zwodev/vm1-video-mixer/vm1/cpp/tests/stb-test/rendered-tiles/Cousine-Regular.png

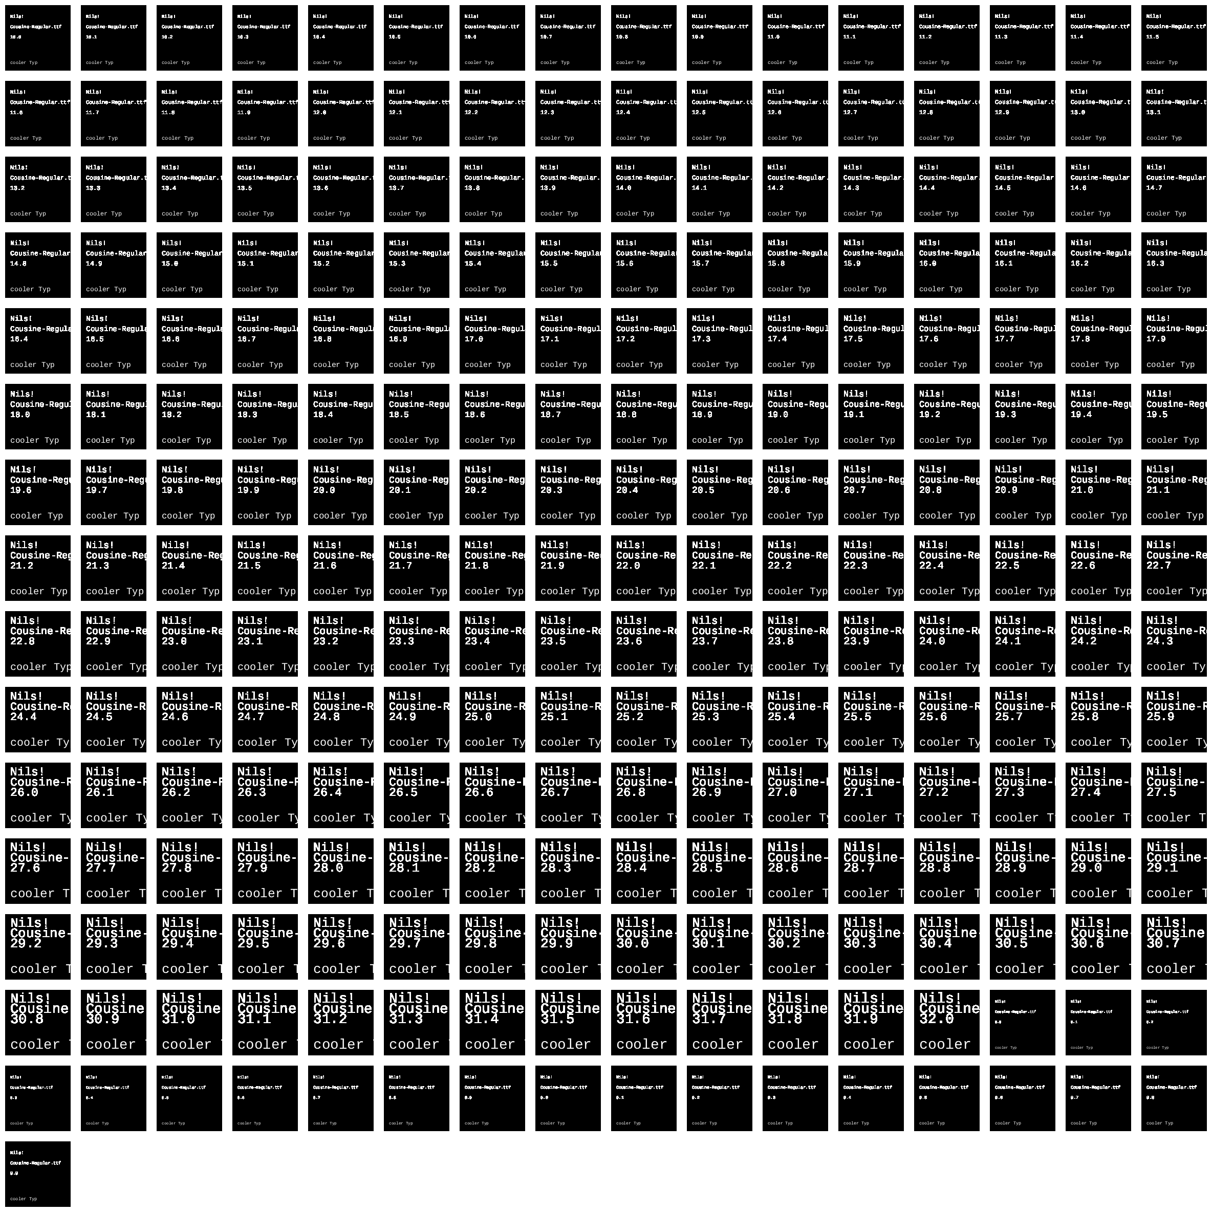
vm1/cpp/tests/stb-test/rendered-tiles/Cousine-Regular.png
