zwodev/vm1-video-mixer/vm1/cpp/source/DeviceController.cpp

/*
 * Copyright (c) 2023-2026 Nils Zweiling & Julian Jungel
 *
 * This file is part of VM-1 which is released under the MIT license.
 * See file LICENSE or go to https://github.com/zwodev/vm1-video-mixer/tree/master/LICENSE
 * for full license details.
 */

#include "DeviceController.h"
#include "VM1DeviceDefinitions.h"
#include <string>
#include <iostream>
#include <fcntl.h>
#include <termios.h>
#include <unistd.h>
#include <cstring>
#include <lgpio.h>

DeviceController::DeviceController(EventBus& eventBus, Registry& registry) : 
    m_eventBus(eventBus),
    m_registry(registry)
{}

DeviceController::~DeviceController(){
    disconnect();
}

// Helper: Set up serial port
bool DeviceController::connect(const std::string& port)
{
    //bool isProVersion = false;

    std::cout << "Failed to open Serial Connection, trying I2C..." << std::endl;
    if(connectI2C()) 
    {
        std::cout << "Connected to VM1-Device via I2C." << std::endl;
        //isProVersion = true;
    } 
    else
    {
        std::cout << "Failed to open I2C, using standard keyboard mode." << std::endl;
        return false;
    }    

    //m_registry.settings().isProVersion = isProVersion;
    return true;
}


bool DeviceController::connectI2C()
{
    m_gpioHandler = lgGpiochipOpen(0); // Usually GPIO chip 0 is correct
    if (m_gpioHandler < 0)
    {
        std::cerr << "Failed to open gpiochip\n";
        return false;
    }
    
    m_i2c_handle = lgI2cOpen(1, 0x08, 0); // bus 1, address 0x08
    if (m_i2c_handle < 0)
    {
        std::cerr << "Failed to open I2C device\n";
        return false;
    }
    return true;
}

void DeviceController::disconnect()
{


    if(m_i2c_handle >= 0)
    {
        lgI2cClose(m_i2c_handle);
        m_i2c_handle = -1;
        
    }

    if (m_gpioHandler >= 0) {
        lgGpiochipClose(m_gpioHandler);
        m_gpioHandler = -1;
    }
}
     

void DeviceController::send(const VM1DeviceState& vm1DeviceState)
{
    // Do not send state when nothing has changed (aka hash is the same)
    size_t hash = vm1DeviceState.hash();
    if (hash == m_lastHash)
        return;

    m_lastHash = hash;

    if (m_i2c_handle >= 0) 
    {
        lgI2cWriteDevice(m_i2c_handle, reinterpret_cast<const char*>(&vm1DeviceState), sizeof(VM1DeviceState));
    }

}

void DeviceController::requestVM1DeviceBuffer() 
{
    if(m_i2c_handle < 0) return;
    
    DeviceBuffer deviceBuffer;
    int count = lgI2cReadDevice(m_i2c_handle, reinterpret_cast<char*>(&deviceBuffer), sizeof(DeviceBuffer));
    if (count != sizeof(DeviceBuffer))
    {
        std::cerr << "Failed to read from I2C device\n";
    }
    else
    {
        bool isFnPressed = deviceBuffer.fnPressed;
        int buttonId = -1;

        for(uint8_t i = 0; i < sizeof(deviceBuffer.buttonEvents)/sizeof(ButtonEvent); i++)
        {
            buttonId = deviceBuffer.buttonEvents[i].buttonId;

            if(!isFnPressed) // if FN not pressed
            {
                switch(deviceBuffer.buttonEvents[i].eventType) 
                {
                    case EDIT_BUTTON_EVENT:
                        m_eventBus.publish(EditModeEvent(buttonId));
                        break;
                    case MEDIA_BUTTON_EVENT: {
                        int mediaSlotId = (m_registry.inputMappings().focusedBank * MEDIA_BUTTON_COUNT) + buttonId;
                        m_eventBus.publish(MediaSlotEvent(mediaSlotId, true));
                        break; }

                    case NAVIGATION_BUTTON_EVENT:
                        if(buttonId == NAVIGATION_BUTTON_RIGHT)
                        {
                            m_eventBus.publish(NavigationEvent(NavigationEvent::Type::NavigationEnter));
                        }
                        else if (buttonId == NAVIGATION_BUTTON_LEFT)
                        {
                            m_eventBus.publish(NavigationEvent(NavigationEvent::Type::NavigationExit));
                        }
                        break;
                    case ROTARY_EVENT:
                        if (buttonId == PRIMARY_ENCODER_CCW)
                        {
                            m_eventBus.publish(NavigationEvent(NavigationEvent::Type::NavigationUp));
                        }
                        else if (buttonId == PRIMARY_ENCODER_CW)
                        {
                            m_eventBus.publish(NavigationEvent(NavigationEvent::Type::NavigationDown));
                        }
                        else if (buttonId == SECONDARY_ENCODER_CCW)
                        {
                            m_eventBus.publish(NavigationEvent(NavigationEvent::Type::NavigationAuxUp));
                        }
                        else if (buttonId == SECONDARY_ENCODER_CW)
                        {
                            m_eventBus.publish(NavigationEvent(NavigationEvent::Type::NavigationAuxDown));
                        }
                        break;
                    default:                    
                        break;
                }
            }
            else    // if FN pressed
            {
                switch(deviceBuffer.buttonEvents[i].eventType) 
                {
                    case EDIT_BUTTON_EVENT:
                        m_eventBus.publish(BankChangeEvent(buttonId));
                        break;
                    case MEDIA_BUTTON_EVENT: {
                        int mediaSlotId = (m_registry.inputMappings().focusedBank * MEDIA_BUTTON_COUNT) + buttonId;
                        m_eventBus.publish(MediaSlotEvent(mediaSlotId, false));
                        break; }

                    case NAVIGATION_BUTTON_EVENT:
                        if(buttonId == NAVIGATION_BUTTON_RIGHT)
                        {
                            m_eventBus.publish(ValueChangeEvent(ValueChangeEvent::Type::Up, 0));
                        }
                        else if (buttonId == NAVIGATION_BUTTON_LEFT)
                        {
                            m_eventBus.publish(ValueChangeEvent(ValueChangeEvent::Type::Down, 0));
                        }
                        break;
                    case ROTARY_EVENT:
                        if (buttonId == PRIMARY_ENCODER_CCW)
                        {
                            m_eventBus.publish(ValueChangeEvent(ValueChangeEvent::Type::Down, 0));
                        }
                        else if (buttonId == PRIMARY_ENCODER_CW)
                        {
                            m_eventBus.publish(ValueChangeEvent(ValueChangeEvent::Type::Up, 0));
                        }
                        else if (buttonId == SECONDARY_ENCODER_CCW)
                        {
                            m_eventBus.publish(ValueChangeEvent(ValueChangeEvent::Type::Down, 1));
                        }
                        else if (buttonId == SECONDARY_ENCODER_CW)
                        {
                            m_eventBus.publish(ValueChangeEvent(ValueChangeEvent::Type::Up, 1));
                        }
                    default:                    
                        break;
                }
            }

            // switch(deviceBuffer.buttonEvents[i].eventType) 
            // {
            //     case EDIT_BUTTON_EVENT:
            //         isFnPressed ? m_eventBus.publish(BankChangeEvent(buttonId))
            //                     : m_eventBus.publish(EditModeEvent(buttonId));
            //         break;
            //     case MEDIA_BUTTON_EVENT: {
            //         int mediaSlotId = (m_registry.inputMappings().focusedBank * MEDIA_BUTTON_COUNT) + buttonId;
            //         m_eventBus.publish(MediaSlotEvent(mediaSlotId, !isFnPressed));
            //         break; }
            //     case NAVIGATION_BUTTON_EVENT:
            //         if(buttonId == NAVIGATION_BUTTON_LEFT)
            //         {
            //             isFnPressed ?  m_eventBus.publish(NavigationEvent(NavigationEvent::Type::FnNavigationLeft))
            //                          : m_eventBus.publish(NavigationEvent(NavigationEvent::Type::NavigationLeft));
            //         }
            //         else if (buttonId == NAVIGATION_BUTTON_RIGHT)
            //         {
            //             isFnPressed ?  m_eventBus.publish(NavigationEvent(NavigationEvent::Type::FnNavigationRight))
            //                          : m_eventBus.publish(NavigationEvent(NavigationEvent::Type::NavigationRight));
            //         }
            //         else 
            //         {
            //             printf("Unknown Navigation Button Id #%d\n", buttonId);
            //         }
            //         break;
            //     case ROTARY_EVENT:
            //         if (buttonId == PRIMARY_ENCODER_CCW)
            //         {
            //             isFnPressed ? m_eventBus.publish(ValueChangeEvent(ValueChangeEvent::Type::Down, 0)) 
            //                         : m_eventBus.publish(NavigationEvent(NavigationEvent::Type::NavigationUp));
            //         }
            //         else if (buttonId == PRIMARY_ENCODER_CW)
            //         {
            //             isFnPressed ? m_eventBus.publish(ValueChangeEvent(ValueChangeEvent::Type::Up, 0)) 
            //                         : m_eventBus.publish(NavigationEvent(NavigationEvent::Type::NavigationDown));
            //         }
            //         else if (buttonId == SECONDARY_ENCODER_CCW)
            //         {
            //             isFnPressed ? m_eventBus.publish(ValueChangeEvent(ValueChangeEvent::Type::Down, 1)) 
            //                         : m_eventBus.publish(NavigationEvent(NavigationEvent::Type::NavigationAuxUp));
            //         }
            //         else if (buttonId == SECONDARY_ENCODER_CW)
            //         {
            //             isFnPressed ? m_eventBus.publish(ValueChangeEvent(ValueChangeEvent::Type::Up, 1)) 
            //                         : m_eventBus.publish(NavigationEvent(NavigationEvent::Type::NavigationAuxDown));
            //         }
            //         else
            //         {
            //             printf("Unknown Rotary Button Id #%d\n", buttonId);
            //         }
            //         break;
            //     default:
                
            //         break;
            // }
        }
        if (deviceBuffer.buttonEvents->eventType != NO_EVENT)
            m_eventBus.publish(SystemEvent(SystemEvent::KeyDown)); // used for time-out in kiosk mode


        // quick solution to get analogInput[0]
        float analogIn = float(deviceBuffer.analogInput[0]) / 1024.0;
        if (analogIn < 0.01) analogIn = 0.0;
        else if (analogIn > 0.99) analogIn = 1.0;
        m_registry.settings().analog0 = analogIn;

        // quick solution to get analogInput[1]
        analogIn = float(deviceBuffer.analogInput[1]) / 1024.0;
        if (analogIn < 0.01) analogIn = 0.0;
        else if (analogIn > 0.99) analogIn = 1.0;
        m_registry.settings().analog1 = analogIn;

        // quick solution to get analogInput[2]
        analogIn = float(deviceBuffer.analogInput[2]) / 1024.0;
        if (analogIn < 0.01) analogIn = 0.0;
        else if (analogIn > 0.99) analogIn = 1.0;
        m_registry.settings().analog2 = analogIn;

        // quick solution to get analogInput[3]
        analogIn = float(deviceBuffer.analogInput[3]) / 1024.0;
        if (analogIn < 0.01) analogIn = 0.0;
        else if (analogIn > 0.99) analogIn = 1.0;
        m_registry.settings().analog3 = analogIn;
    }
}
