zwodev/vm1-video-mixer/vm1/cpp/source/CameraController.cpp

/*
 * Copyright (c) 2023-2026 Nils Zweiling & Julian Jungel
 *
 * This file is part of VM-1 which is released under the MIT license.
 * See file LICENSE or go to https://github.com/zwodev/vm1-video-mixer/tree/master/LICENSE
 * for full license details.
 */

#include "CameraController.h"
#include <SDL3/SDL.h>
#include "edid/1080p30edid.h"

#include <dirent.h>
#include <map>

CameraController::CameraController(EventBus& eventBus) :
    m_eventBus(eventBus)
{
    // 
}

CameraController::~CameraController() 
{
    if (m_thread.joinable()) {
        m_thread.join();
    }
}

std::vector<CaptureDevice> CameraController::getCaptureDevices(const std::string& driverName)
{
    std::map<std::string, CaptureDevice> captureDevicesMap;
    DIR* dir = opendir("/dev");
    if (dir == nullptr) {
        return std::vector<CaptureDevice>();
    }

    struct dirent* entry;
    std::vector<std::string> entries;
    while ((entry = readdir(dir)) != nullptr) {
        if (strncmp(entry->d_name, "video", 5) == 0) {
            entries.push_back("/dev/" + std::string(entry->d_name));
        }
    }

    std::sort(entries.begin(), entries.end());

    for (auto entry: entries) {
        int fd = open(entry.c_str(), O_RDONLY);
        if (fd == -1) {
            continue;
        }

        struct v4l2_capability cap;
        if (ioctl(fd, VIDIOC_QUERYCAP, &cap) == -1) {
            close(fd);
            continue;
        }

        close(fd);
        
        if ((cap.capabilities & V4L2_CAP_VIDEO_CAPTURE) && (cap.capabilities & V4L2_CAP_DEVICE_CAPS)) {
            std::string busInfo((char*)cap.bus_info);
            std::string driver(std::string((char*)cap.driver));
            if (driver == driverName && captureDevicesMap.find(busInfo) == captureDevicesMap.end()) {
                CaptureDevice captureDevice;
                captureDevice.devicePath = entry;
                captureDevice.name = std::string((char*)cap.card);
                captureDevice.driver = driver;
                captureDevice.busInfo = busInfo;
                captureDevicesMap[busInfo] = captureDevice;
            }
        }
    } 

    closedir(dir);

    std::vector<CaptureDevice> captureDevices;
    for (const auto& capDev : captureDevicesMap) {
        captureDevices.push_back(capDev.second);
    }
    return captureDevices;
}

void CameraController::setupDetached(bool useUvcCaptureDevice)
{
    if (m_thread.joinable()) {
        m_thread.join();
    }

    if (useUvcCaptureDevice) {
         m_thread = std::thread(&CameraController::setupUVC, this);
    }
    else {
        m_thread = std::thread(&CameraController::setupCSI, this);
    }
}

bool CameraController::setupUVC()
{
    auto captureDevices = getCaptureDevices("uvcvideo");
    for (auto& captureDevice : captureDevices) {
        captureDevice.label = "1920x1080/Auto";
    }
    if (captureDevices.size() < 2) {
        captureDevices.resize(2, CaptureDevice());
    }
    m_eventBus.enqueue(HdmiCaptureInitEvent(captureDevices));

    // if (captureDevices.size() > 0) {
    //     CaptureDevice captureDevice = captureDevices[0];
    //     m_eventBus.enqueue(HdmiCaptureInitEvent(std::string("1920x1080/Auto"), captureDevice.devicePath));
    //     return true;
    // }
    // m_eventBus.enqueue(HdmiCaptureInitEvent(std::string("Not connected")));
    
    
    return false;
}

bool CameraController::setupCSI() 
{
    std::vector<CaptureDevice> outputCaptureDevices(2, CaptureDevice());

    std::string devicePath;
    auto captureDevices = getCaptureDevices("rp1-cfe");
    if (captureDevices.size() > 0) {
        CaptureDevice captureDevice = captureDevices[0];
        devicePath = captureDevice.devicePath;
    }

    v4l2_dv_timings timings;
    std::string subdevPath;
    const std::string captureDeviceName = "rp1-cfe";
    std::string mediaPath = MediaController::getDevicePath(captureDeviceName);
    if (mediaPath.empty()) {
        std::cout << "Could not find capture device: " <<  captureDeviceName << std::endl;        
        goto unknownerror;
    }

    // Media Controller
    if (!m_mediaController.openDevice(mediaPath)) goto unknownerror;
    if (!m_mediaController.getTopology()) goto unknownerror;
    //m_mediaController.printTopology();

    // V4L2 Controller
    subdevPath = m_mediaController.getSubdeviceFromName("tc358743");
    if (!m_v4l2Controller.openDevice(subdevPath)) goto unknownerror;
    if (!m_v4l2Controller.setEdid(edid_1080p30)) goto unknownerror;
    SDL_Delay(5000);
    if (!m_v4l2Controller.setDvTimings()) goto notconnected;
    timings =  m_v4l2Controller.queryDvTimings();
    if (timings.bt.width == 0 && timings.bt.height == 0) {
        goto notconnected;
    }
    else if (timings.bt.width != 1920 || timings.bt.height != 1080) {
        goto resmismatch;
    }
    else if (timings.bt.pixelclock != 74250000) {
        goto fpsmismatch;
    }

    m_v4l2Controller.printDvTimings(timings);
    m_v4l2Controller.closeDevice();
    
    //if (!m_mediaController.resetLinks()) return false;
    if (!m_mediaController.setupLink("csi2", "rp1-cfe-csi2_ch0", MEDIA_LNK_FL_ENABLED)) goto unknownerror;
    m_mediaController.closeDevice();

    if (!m_mediaController.setFormat("csi2", 0, "UYVY8_1X16", 1920, 1080)) goto unknownerror;
    if (!m_mediaController.setFormat("csi2", 4, "UYVY8_1X16", 1920, 1080)) goto unknownerror;
    if (!m_mediaController.setFormat("tc358743", 0, "UYVY8_1X16", 1920, 1080)) goto unknownerror;
    
    
    outputCaptureDevices[0].label = "1920x1080/30Hz";
    outputCaptureDevices[0].devicePath = devicePath;
    m_eventBus.enqueue(HdmiCaptureInitEvent(outputCaptureDevices));
    return true;

    notconnected:
    outputCaptureDevices[0].label = "Not connected";
    m_eventBus.enqueue(HdmiCaptureInitEvent(outputCaptureDevices));
    m_v4l2Controller.closeDevice();
    m_mediaController.closeDevice();
    return false;

    resmismatch:
    outputCaptureDevices[0].label = "RES mismatch";
    m_eventBus.enqueue(HdmiCaptureInitEvent(outputCaptureDevices));
    m_v4l2Controller.closeDevice();
    m_mediaController.closeDevice();
    return false;

    fpsmismatch:
    outputCaptureDevices[0].label = "FPS mismatch";
    m_eventBus.enqueue(HdmiCaptureInitEvent(outputCaptureDevices));  
    m_v4l2Controller.closeDevice();
    m_mediaController.closeDevice();
    return false;  
        
    unknownerror:
    outputCaptureDevices[0].label = "Unknown error";
    m_eventBus.enqueue(HdmiCaptureInitEvent(outputCaptureDevices));   
    m_v4l2Controller.closeDevice();
    m_mediaController.closeDevice();
    
    return false;
}
