zwodev/vm1-video-mixer/vm1-device/arduino/VM1Device/src/RotaryEncoder.h

#ifndef ROTARYENCODER_H
#define ROTARYENCODER_H

#include <stdint.h>
#include "pico/stdlib.h"
#include "DeviceBufferController.h"

#define ROTARY_0_PIN_A 19
#define ROTARY_0_PIN_B 18
#define ROTARY_1_PIN_A 17
#define ROTARY_1_PIN_B 16

typedef struct
{
  uint8_t pin_a;
  uint8_t pin_b;
  int32_t position;
  volatile uint8_t last_stable_state; // last debounced stable state
  volatile uint8_t last_read_state;   // last raw read state
  volatile uint32_t last_change_us;   // last time state changed (micros)
  volatile bool state_changed_flag;   // set by ISR, processed outside

} rotary_encoder_t;

void initRotaryEncoders();
void updateRotaryEncoders();

void rotary_encoder_init(rotary_encoder_t *enc);
int8_t rotary_encoder_process(rotary_encoder_t *enc, int32_t &position);
void gpio_callback(uint gpio, uint32_t events);

#endif
