zwodev/vm1-video-mixer/vm1/cpp/source/VideoPlayer.cpp

/*
 * Copyright (c) 2023-2026 Nils Zweiling & Julian Jungel
 *
 * This file is part of VM-1 which is released under the MIT license.
 * See file LICENSE or go to https://github.com/zwodev/vm1-video-mixer/tree/master/LICENSE
 * for full license details.
 * 
 * Parts of this file have been taken from:
 * https://github.com/libsdl-org/SDL/blob/main/test/testffmpeg.c
 * 
 */

#include "source/GLHelper.h"
#include "source/VideoPlayer.h"

#include <SDL3/SDL_opengl.h>
#include <SDL3/SDL_opengles2.h>
#include <EGL/eglext.h>
#include <GLES3/gl31.h>

#ifndef fourcc_code
#define fourcc_code(a, b, c, d) ((uint32_t)(a) | ((uint32_t)(b) << 8) | ((uint32_t)(c) << 16) | ((uint32_t)(d) << 24))
#endif
#ifndef DRM_FORMAT_R8
#define DRM_FORMAT_R8 fourcc_code('R', '8', ' ', ' ')
#endif
#ifndef DRM_FORMAT_GR88
#define DRM_FORMAT_GR88 fourcc_code('G', 'R', '8', '8')
#endif
#ifndef DRM_FORMAT_RGBA8888
#define DRM_FORMAT_RGBA8888 fourcc_code('R', 'A', '2', '4')
#endif

VideoPlayer::VideoPlayer()
{
    m_numberOfInputImages = 15;
    loadShaders();
    createVertexBuffers();
    initializeFramebufferAndTextures();
}

VideoPlayer::~VideoPlayer()
{
    close();
}

void VideoPlayer::setInPoint(double value)
{
    m_inPoint = value;
}

double VideoPlayer::inPoint()
{
    return m_inPoint;
}

void VideoPlayer::setOutPoint(double value)
{
    m_outPoint = value;
}

double VideoPlayer::outPoint()
{
    return m_outPoint;
}

void VideoPlayer::reset()
{
    MediaPlayer::reset();
    m_startTime = 0;
    m_firstPts = -1.0;
    m_firstAudioPts = -1.0;
    m_isFlushing = false;
    m_foundKeyframe = false;
    m_currentTime = 0.0;
}

void VideoPlayer::pause(bool isPaused) {
    if (isPaused && !m_isPaused)
        m_pauseStartTime = SDL_GetTicks();
    else if (!isPaused && m_isPaused)
        m_startTime += SDL_GetTicks() - m_pauseStartTime;
    m_isPaused = isPaused;
}


void VideoPlayer::loadShaders()
{
    m_shader.load("shaders/video.vert", "shaders/video.frag");
}

bool VideoPlayer::openFile(const std::string& fileName, AudioStream* audioStream)
{
    close(); 
    
    // This is just for rtsp steams. Necessary?
    //AVDictionary* opts = NULL;
    //av_dict_set(&opts, "rtsp_transport", "tcp", 0);

    // Open the video file
    int result = avformat_open_input(&m_formatContext, fileName.c_str(), NULL, NULL);
    if (result < 0) {
        SDL_LogError(SDL_LOG_CATEGORY_APPLICATION, "Couldn't open %s: %d", fileName.c_str(), result);
        return false;
    }

    if (avformat_find_stream_info(m_formatContext, NULL) < 0) {
        SDL_LogError(SDL_LOG_CATEGORY_APPLICATION, "Couldn't find stream info in file %s: %d", fileName.c_str(), result);
        return false; 
    }

    bool foundStream = false;
    for (unsigned int i = 0; i < m_formatContext->nb_streams; i++) {
        AVStream *stream = m_formatContext->streams[i];
        AVCodecParameters *codecpar = stream->codecpar;
        if (codecpar->codec_type == AVMEDIA_TYPE_VIDEO &&
            codecpar->width == 1920 &&
            codecpar->height == 1080 &&
            codecpar->codec_id == AV_CODEC_ID_HEVC &&
            (codecpar->format == AV_PIX_FMT_YUV420P || codecpar->format == AV_PIX_FMT_YUVJ420P) &&
            codecpar->color_space != AVCOL_SPC_BT2020_NCL &&
            codecpar->color_space != AVCOL_SPC_BT2020_CL
        )
        {
            foundStream = true;
            m_width = codecpar->width;
            m_height = codecpar->height;
            std::cout << "***** CODEC: color_primaries: " << codecpar->color_primaries << std::endl;
            std::cout << "***** CODEC: color_trc: " << codecpar->color_trc << std::endl;
            std::cout << "***** CODEC: color_space: " << codecpar->color_space << std::endl;
            break;
        }
    }

    if (!foundStream) {
        SDL_LogError(SDL_LOG_CATEGORY_APPLICATION, "Couldn't find a valid HEVC/1080p video stream in file %s: %d", fileName.c_str(), result);
        return false;
    }

    m_videoStream = av_find_best_stream(m_formatContext, AVMEDIA_TYPE_VIDEO, -1, -1, &m_videoCodec, 0);
    if (m_videoStream >= 0) {
        m_fps = av_q2d(m_formatContext->streams[m_videoStream]->avg_frame_rate);
        m_duration = m_formatContext->streams[m_videoStream]->duration * av_q2d(m_formatContext->streams[m_videoStream]->time_base);

        m_videoContext = openVideoStream();
        if (!m_videoContext) {
            return false;
        }
    }

    m_audioStream = av_find_best_stream(m_formatContext, AVMEDIA_TYPE_AUDIO, -1, m_videoStream, &m_audioCodec, 0);
    
    // This is just for rtsp steams. Necessary?
    //m_formatContext->max_analyze_duration = 5 * AV_TIME_BASE;
    //m_formatContext->probesize = 5 * 1024 * 1024;
    //av_dump_format(m_formatContext, 0, "format_dump.txt", 0);

    m_audio = audioStream;
    if (m_audioStream >= 0) {
        m_audioContext = openAudioStream();
        if (!m_audioContext) {
            return false;
        }
    }

    m_packet = av_packet_alloc();
    if (!m_packet) {
        SDL_LogError(SDL_LOG_CATEGORY_APPLICATION, "av_packet_alloc failed");
        return false;
    }
    m_frame = av_frame_alloc();
    if (!m_frame) {
        SDL_LogError(SDL_LOG_CATEGORY_APPLICATION, "av_frame_alloc failed");
        return false;
    }

    return true;
}

void VideoPlayer::close()
{
    MediaPlayer::close();
    if (m_packet) {
        av_packet_free(&m_packet);
        m_packet = nullptr;
    }
    if (m_frame) {
        av_frame_free(&m_frame);
        m_frame = nullptr;
    }
    if (m_audioContext) {
        avcodec_free_context(&m_audioContext);
        m_audioContext = nullptr;
    }
    if (m_videoContext) {
        avcodec_free_context(&m_videoContext);
        m_videoContext = nullptr;
    }
    if (m_formatContext) {
        avformat_close_input(&m_formatContext);
        m_formatContext = nullptr;
    }

    m_audioCodec = nullptr;
    m_videoCodec = nullptr;
}

void VideoPlayer::setLooping(bool looping)
{
    m_isLooping = looping;
}

AVCodecContext* VideoPlayer::openVideoStream()
{
    AVStream *st = m_formatContext->streams[m_videoStream];
    AVCodecParameters *codecpar = st->codecpar;
    AVCodecContext *context;
    const AVCodecHWConfig *config;
    enum AVHWDeviceType type;
    int i;
    int result;

    SDL_Log("Video stream: %s %dx%d\n", avcodec_get_name(m_videoCodec->id), codecpar->width, codecpar->height);

    context = avcodec_alloc_context3(NULL);
    if (!context) {
        SDL_LogError(SDL_LOG_CATEGORY_APPLICATION, "avcodec_alloc_context3 failed");
        return NULL;
    }

    result = avcodec_parameters_to_context(context, m_formatContext->streams[m_videoStream]->codecpar);
    if (result < 0) {
        //SDL_LogError(SDL_LOG_CATEGORY_APPLICATION, "avcodec_parameters_to_context failed: %s\n", av_err2str(result));
        avcodec_free_context(&context);
        return NULL;
    }
    context->pkt_timebase = m_formatContext->streams[m_videoStream]->time_base;

    /* Look for supported hardware accelerated configurations */
    i = 0;
    while (!context->hw_device_ctx &&
           (config = avcodec_get_hw_config(m_videoCodec, i++)) != NULL) {
        
        SDL_Log("Found %s hardware acceleration with pixel format %s\n", av_hwdevice_get_type_name(config->device_type), av_get_pix_fmt_name(config->pix_fmt));

        if (!(config->methods & AV_CODEC_HW_CONFIG_METHOD_HW_DEVICE_CTX) ||
            !isSupportedPixelFormat(config->pix_fmt)) {
            continue;
        }

        type = AV_HWDEVICE_TYPE_NONE;
        while (!context->hw_device_ctx &&
               (type = av_hwdevice_iterate_types(type)) != AV_HWDEVICE_TYPE_NONE) {
            if (type != config->device_type) {
                continue;
            }

            {
                result = av_hwdevice_ctx_create(&context->hw_device_ctx, type, NULL, NULL, 0);
                if (result < 0) {
                    //SDL_LogError(SDL_LOG_CATEGORY_APPLICATION, "Couldn't create hardware device context: %s", av_err2str(result));
                } else {
                    SDL_Log("Using %s hardware acceleration with pixel format %s\n", av_hwdevice_get_type_name(config->device_type), av_get_pix_fmt_name(config->pix_fmt));
                }
            }
        }
    }

    /* Allow supported hardware accelerated pixel formats */
    context->get_format = getSupportedPixelFormat;

    result = avcodec_open2(context, m_videoCodec, NULL);
    if (result < 0) {
        //SDL_LogError(SDL_LOG_CATEGORY_APPLICATION, "Couldn't open codec %s: %s", avcodec_get_name(context->codec_id), av_err2str(result));
        avcodec_free_context(&context);
        return nullptr;
    }

    return context;
}

AVCodecContext* VideoPlayer::openAudioStream()
{
    AVStream *st = m_formatContext->streams[m_audioStream];
    AVCodecParameters *codecpar = st->codecpar;
    AVCodecContext *context;
    int result;

    SDL_Log("Audio stream: %s %d channels, %d Hz\n", avcodec_get_name(m_audioCodec->id), codecpar->ch_layout.nb_channels, codecpar->sample_rate);

    context = avcodec_alloc_context3(nullptr);
    if (!context) {
        SDL_LogError(SDL_LOG_CATEGORY_APPLICATION, "avcodec_alloc_context3 failed\n");
        return nullptr;
    }

    result = avcodec_parameters_to_context(context, m_formatContext->streams[m_audioStream]->codecpar);
    if (result < 0) {
       // SDL_LogError(SDL_LOG_CATEGORY_APPLICATION, "avcodec_parameters_to_context failed: %s\n", av_err2str(result));
        avcodec_free_context(&context);
        return nullptr;
    }
    context->pkt_timebase = m_formatContext->streams[m_audioStream]->time_base;

    result = avcodec_open2(context, m_audioCodec, NULL);
    if (result < 0) {
        //SDL_LogError(SDL_LOG_CATEGORY_APPLICATION, "Couldn't open codec %s: %s", avcodec_get_name(context->codec_id), av_err2str(result));
        avcodec_free_context(&context);
        return nullptr;
    }

    if (m_audio) {
        SDL_AudioSpec spec = { SDL_AUDIO_F32, codecpar->ch_layout.nb_channels, codecpar->sample_rate };
        m_audio->createAndBind(spec);   
    }

    return context;
}

void VideoPlayer::render()
{
    glViewport(0, 0, 1920, 1080);
    // TODO: resize framebuffer if necessary
    glBindFramebuffer(GL_FRAMEBUFFER, m_frameBuffer);
    glClearColor(0.1f, 0.1f, 0.1f, 1.0f);
    glClear(GL_COLOR_BUFFER_BIT);

    float stripCount = truncf((float(m_width) / 128.0f) + 0.5f); 
    //float stripCount = 15.0f;

    m_shader.activate();
    m_shader.setValue("stripWidthNDC", 2.0f/stripCount);

    glBindVertexArray(m_vao);
    for (size_t i = 0; i < m_yuvTextures.size(); ++i) {
        glActiveTexture(GL_TEXTURE0);
        glBindTexture(GL_TEXTURE_2D, m_yuvTextures[i]);
        glTexParameteri(GL_TEXTURE_2D, GL_TEXTURE_MIN_FILTER, GL_NEAREST);
        glTexParameteri(GL_TEXTURE_2D, GL_TEXTURE_MAG_FILTER, GL_NEAREST);
        glTexParameteri(GL_TEXTURE_2D, GL_TEXTURE_WRAP_S, GL_CLAMP_TO_EDGE);
        glTexParameteri(GL_TEXTURE_2D, GL_TEXTURE_WRAP_T, GL_CLAMP_TO_EDGE);

        // Bind the texture to unit
        if (m_yuvImages[i] != EGL_NO_IMAGE) {
            GLHelper::glEGLImageTargetTexture2DOESFunc(GL_TEXTURE_2D, m_yuvImages[i]);
            m_shader.bindUniformLocation("inputTexture", 0);
        }

        m_shader.setValue("stripId", static_cast<int>(i));
        glDrawArrays(GL_TRIANGLES, 0, 6);
    }

    glBindVertexArray(0);
    m_shader.deactivate();

    glBindTexture(GL_TEXTURE_2D, 0);
    glBindFramebuffer(GL_FRAMEBUFFER, 0);
}

void VideoPlayer::update()
{
    if (!m_isRunning || m_isPaused) return;
    
    EGLDisplay display = eglGetCurrentDisplay();

    // Wait for fence and delete it
    eglClientWaitSync(display, m_fence, EGL_SYNC_FLUSH_COMMANDS_BIT, EGL_FOREVER);
    eglDestroySync(display, m_fence);
    m_fence = EGL_NO_SYNC;

    // TODO: Can EGLImages be reused? It seems like the DRM-Buf FDs change very often.
    for (auto& yuvImage : m_yuvImages ) {
        if (yuvImage != nullptr) {
            eglDestroyImage(display, yuvImage);
            yuvImage = nullptr;
        }
    }

    VideoFrame videoFrame;
    
    bool processVideoFrame = true;
    if (m_videoQueue.peekFrame(videoFrame)) {
        if (videoFrame.isFirstFrame) m_startTime = SDL_GetTicks();

        double pts = videoFrame.pts;
        double now = (double)(SDL_GetTicks() - m_startTime) / 1000.0;
        
        // Do not pop and display frame when PTS is ahead 
        if (now < (pts - 0.001)) processVideoFrame = false; 
    }

    if (processVideoFrame && m_videoQueue.popFrame(videoFrame)) {
        // Create EGL images here in the main thread
        // TODO: Support for multiple planes and images (see older version)
        for (size_t i = 0; i < m_yuvImages.size(); ++i) {
            if (videoFrame.formats.size() > 0) {
                int j = 0;
                int height = videoFrame.heights[j] + (videoFrame.heights[j] / 2);
                EGLAttrib img_attr[] = {
                    EGL_LINUX_DRM_FOURCC_EXT,      videoFrame.formats[j],
                    EGL_WIDTH,                     128,
                    EGL_HEIGHT,                    height,
                    EGL_DMA_BUF_PLANE0_FD_EXT,     videoFrame.fds[j],
                    EGL_DMA_BUF_PLANE0_OFFSET_EXT, static_cast<int>(i) * 128 * height,
                    EGL_DMA_BUF_PLANE0_PITCH_EXT,  128,
                    EGL_NONE
                };
                
                EGLImage image = eglCreateImage(display, EGL_NO_CONTEXT, EGL_LINUX_DMA_BUF_EXT, NULL, img_attr);
                if (image != EGL_NO_IMAGE) {
                    m_yuvImages[i] = image;
                }
            }
        }
    }

    if (m_audio) {
        AudioFrame audioFrame;
        while (m_audioQueue.peekFrame(audioFrame)) {
            if (m_audioQueue.popFrame(audioFrame)) {
                m_audio->putData(audioFrame.data);
            }
        }
    }

    if (processVideoFrame) {
        render();
        // m_currentTime = m_firstPts + videoFrame.pts;
        m_currentTime = videoFrame.absolutePts;
        m_fence = eglCreateSync(display, EGL_SYNC_FENCE, NULL);
    }
}

static SDL_AudioFormat GetAudioFormat(int format)
{
    switch (format) {
    case AV_SAMPLE_FMT_U8:
    case AV_SAMPLE_FMT_U8P:
        return SDL_AUDIO_U8;
    case AV_SAMPLE_FMT_S16:
    case AV_SAMPLE_FMT_S16P:
        return SDL_AUDIO_S16;
    case AV_SAMPLE_FMT_S32:
    case AV_SAMPLE_FMT_S32P:
        return SDL_AUDIO_S32;
    case AV_SAMPLE_FMT_FLT:
    case AV_SAMPLE_FMT_FLTP:
        return SDL_AUDIO_F32;
    default:
        /* Unsupported */
        return SDL_AUDIO_UNKNOWN;
    }
}

static bool IsPlanarAudioFormat(int format)
{
    switch (format) {
    case AV_SAMPLE_FMT_U8P:
    case AV_SAMPLE_FMT_S16P:
    case AV_SAMPLE_FMT_S32P:
    case AV_SAMPLE_FMT_FLTP:
    case AV_SAMPLE_FMT_DBLP:
    case AV_SAMPLE_FMT_S64P:
        return true;
    default:
        return false;
    }
}

void VideoPlayer::handleAudioFrame(AVFrame *frame)
{
    double pts = ((double)frame->pts * m_audioContext->pkt_timebase.num) / m_audioContext->pkt_timebase.den;
    if (m_firstAudioPts < 0.0) {
        m_firstAudioPts = pts;
    }
    pts -= m_firstAudioPts;
    
    AudioFrame audioFrame;
    audioFrame.pts = pts;
    
    audioFrame.spec = { GetAudioFormat(frame->format), frame->ch_layout.nb_channels, frame->sample_rate };
    int samplesize = SDL_AUDIO_BYTESIZE(GetAudioFormat(frame->format));
    int framesize = SDL_AUDIO_FRAMESIZE(audioFrame.spec);
    audioFrame.data.resize(frame->nb_samples * framesize);

    if (frame->ch_layout.nb_channels > 1 && IsPlanarAudioFormat(frame->format)) {
        // Interleave audio
        for (int c = 0; c < frame->ch_layout.nb_channels; ++c) {
            const Uint8 *src = frame->data[c];
            Uint8 *dst = audioFrame.data.data() + c * samplesize;
            for (int n = 0; n < frame->nb_samples; ++n) {
                SDL_memcpy(dst, src, samplesize);
                src += samplesize;
                dst += framesize;
            }
        }
    } else {
        SDL_memcpy(&(audioFrame.data[0]), frame->data[0], framesize);
    }

    m_audioQueue.pushFrame(audioFrame);
}

void VideoPlayer::seekToInPoint(bool backward) {
    AVStream *stream = m_formatContext->streams[m_videoStream];
    // double dur_s = av_q2d(stream->time_base) * (double)stream->duration;
    // const double loop_start_s = dur_s * double(m_inPoint);
    const double loop_start_s = double(m_inPoint);
    
    int64_t loop_start_pts = llround(loop_start_s / av_q2d(stream->time_base));
    
    int flags = AVSEEK_FLAG_BACKWARD;
    if (av_seek_frame(m_formatContext, m_videoStream, loop_start_pts, flags) >= 0) {
        avcodec_flush_buffers(m_videoContext);
    }
}

void VideoPlayer::run() {
    if (m_inPoint > 0.0) seekToInPoint();

    while (m_isRunning) {
            if (m_isPaused) {
                std::this_thread::sleep_for(std::chrono::milliseconds(5));
                continue;
            }
            if (!m_isFlushing) {
            // Read and decode frames
            int result = av_read_frame(m_formatContext, m_packet);
            if (result < 0) {
                if (m_isLooping) {
                    m_firstPts = -1.0;      
                    seekToInPoint();
                    SDL_Log("End of stream, restart (looping)\n");
                }
                else {
                    SDL_Log("End of stream, finishing decode\n");     
                    m_isFlushing = true;
                }
                if (m_audioContext) {
                    avcodec_flush_buffers(m_audioContext);
                }
                if (m_videoContext) {
                    avcodec_flush_buffers(m_videoContext);
                }
            } else {

                if (m_outPoint > 0.0 && m_packet->stream_index == m_videoStream) {
                    AVStream *stream = m_formatContext->streams[m_videoStream];
                    // double dur_s = av_q2d(stream->time_base) * (double)stream->duration;
                    //const double loop_start_s = dur_s * double(m_inPoint);
                    const double loop_after_s = m_outPoint;
                    
                    //int64_t loop_start_pts = llround(loop_start_s / av_q2d(stream->time_base));
                    int64_t loop_after_pts = llround(loop_after_s / av_q2d(stream->time_base));

                    // Compute packet timestamp (prefer pts, fallback to dts)
                    int64_t pkt_ts = (m_packet->pts != AV_NOPTS_VALUE) ? m_packet->pts : m_packet->dts;
                    if (pkt_ts == AV_NOPTS_VALUE) {
                        av_packet_unref(m_packet);
                        continue;
                    }

                    // If we've reached the out point, either loop back to the in point
                    // or finish decoding, depending on the looping flag.
                    if (pkt_ts >= loop_after_pts) {
                        av_packet_unref(m_packet);
                        if (m_isLooping) {
                            m_firstPts = -1;
                            seekToInPoint(true);
                        } else {
                            m_isFlushing = true;
                        }
                        continue;
                    }

                    // printf("Start: %ld\n", loop_start_pts);
                    // printf("End: %ld\n", loop_after_pts);
                    // printf("Packet: %ld\n", pkt_ts);
                }



                // // This is crucial immediately after a seek: demuxer can return packets earlier than seek_target.
                // if (pkt_ts < loop_start_pts) {
                //     av_packet_unref(m_packet);
                //     continue;
                // }



                //int64_t packet_ts = m_packet->pts == AV_NOPTS_VALUE ? m_packet->dts : m_packet->pts;
                

                // if (m_inPoint > 0.0f) {
                //     AVStream *stream = m_formatContext->streams[m_videoStream];
                //     int64_t duration = stream->duration;
                //     AVRational timebase = stream->time_base;
                //     int64_t start = (int64_t)(m_inPoint * duration);
                //     double start_secs = start * av_q2d(timebase);
                //     int64_t start_ts = (int64_t)(start_secs * AV_TIME_BASE);
                //     packetInRange = duration == AV_NOPTS_VALUE ||
                //         (packet_ts - (start_ts != AV_NOPTS_VALUE ? start_ts : 0)) *
                //         av_q2d(timebase) -
                //         (double)(start_ts != AV_NOPTS_VALUE ? start_ts : 0) / AV_TIME_BASE
                //         <= ((double)duration / AV_TIME_BASE);
                // }

                // printf("InPoint: %f\n", m_inPoint);
    
                if (m_packet->stream_index == m_audioStream) {
                    result = avcodec_send_packet(m_audioContext, m_packet);
                    if (result < 0) {
                        //return;
                    }
                } else if (m_packet->stream_index == m_videoStream) {
                    result = avcodec_send_packet(m_videoContext, m_packet);
                    if (result < 0) {
                        //return;
                    }
                }
                av_packet_unref(m_packet);
            }
        }
        
        if (m_audioContext) {
            while (avcodec_receive_frame(m_audioContext, m_frame) >= 0) {
                if (m_audio) handleAudioFrame(m_frame);
            }
        }
        // Process decoded frames
        if (m_videoContext) { 
            while (avcodec_receive_frame(m_videoContext, m_frame) >= 0) {
                double pts = ((double)m_frame->pts * m_videoContext->pkt_timebase.num) / m_videoContext->pkt_timebase.den;
                bool firstFrame = false;
                if (m_firstPts < 0.0) {
                    m_firstPts = pts;
                    firstFrame = true;
                }

                VideoFrame frame;
                if (getTextureForDRMFrame(m_frame, frame)) {
                    frame.isFirstFrame = firstFrame;
                    frame.pts = pts - m_firstPts;
                    frame.absolutePts = pts;
                    m_videoQueue.pushFrame(frame);
                }
            }
        }

        if (m_isFlushing) m_isRunning = false;
    }
}

bool VideoPlayer::getTextureForDRMFrame(AVFrame* frame, VideoFrame& dstFrame)
{ 
    AVHWFramesContext *frames = (AVHWFramesContext *)(frame->hw_frames_ctx ? frame->hw_frames_ctx->data : NULL);
    const AVDRMFrameDescriptor *desc = (const AVDRMFrameDescriptor *)frame->data[0];

    //printf("%dx%d\n", frames->width, frames->height);

    int imageIndex = 0;
    for (int i = 0; i < desc->nb_layers; ++i) {
        const AVDRMLayerDescriptor *layer = &desc->layers[i];
        for (int j = 0; j < layer->nb_planes; ++j) {
            static const uint32_t formats[2] = { DRM_FORMAT_R8, DRM_FORMAT_GR88 };
            const AVDRMPlaneDescriptor *plane = &layer->planes[j];
            const AVDRMObjectDescriptor *object = &desc->objects[plane->object_index];
            
            // Store DRM frame info instead of creating EGL image
            dstFrame.formats.push_back(formats[j]);
            dstFrame.widths.push_back(frames->width);
            dstFrame.heights.push_back(frames->height);
            dstFrame.fds.push_back(object->fd);
            dstFrame.offsets.push_back(plane->offset);
            dstFrame.pitches.push_back(frames->width);
            imageIndex++;
        }
    }
    return true;
}

SDL_PixelFormat getTextureFormat(enum AVPixelFormat format)
{
    switch (format) {
    case AV_PIX_FMT_RGB8:
        return SDL_PIXELFORMAT_RGB332;
    case AV_PIX_FMT_RGB444:
        return SDL_PIXELFORMAT_XRGB4444;
    case AV_PIX_FMT_RGB555:
        return SDL_PIXELFORMAT_XRGB1555;
    case AV_PIX_FMT_BGR555:
        return SDL_PIXELFORMAT_XBGR1555;
    case AV_PIX_FMT_RGB565:
        return SDL_PIXELFORMAT_RGB565;
    case AV_PIX_FMT_BGR565:
        return SDL_PIXELFORMAT_BGR565;
    case AV_PIX_FMT_RGB24:
        return SDL_PIXELFORMAT_RGB24;
    case AV_PIX_FMT_BGR24:
        return SDL_PIXELFORMAT_BGR24;
    case AV_PIX_FMT_0RGB32:
        return SDL_PIXELFORMAT_XRGB8888;
    case AV_PIX_FMT_0BGR32:
        return SDL_PIXELFORMAT_XBGR8888;
    case AV_PIX_FMT_NE(RGB0, 0BGR):
        return SDL_PIXELFORMAT_RGBX8888;
    case AV_PIX_FMT_NE(BGR0, 0RGB):
        return SDL_PIXELFORMAT_BGRX8888;
    case AV_PIX_FMT_RGB32:
        return SDL_PIXELFORMAT_ARGB8888;
    case AV_PIX_FMT_RGB32_1:
        return SDL_PIXELFORMAT_RGBA8888;
    case AV_PIX_FMT_BGR32:
        return SDL_PIXELFORMAT_ABGR8888;
    case AV_PIX_FMT_BGR32_1:
        return SDL_PIXELFORMAT_BGRA8888;
    case AV_PIX_FMT_YUV420P:
        return SDL_PIXELFORMAT_IYUV;
    case AV_PIX_FMT_YUYV422:
        return SDL_PIXELFORMAT_YUY2;
    case AV_PIX_FMT_UYVY422:
        return SDL_PIXELFORMAT_UYVY;
    case AV_PIX_FMT_NV12:
        return SDL_PIXELFORMAT_NV12;
    case AV_PIX_FMT_NV21:
        return SDL_PIXELFORMAT_NV21;
    case AV_PIX_FMT_P010:
        return SDL_PIXELFORMAT_P010;
    default:
        return SDL_PIXELFORMAT_UNKNOWN;
    }
}

bool isSupportedPixelFormat(enum AVPixelFormat format)
{
    if (/* m_hasEglCreateImage && */
        (format == AV_PIX_FMT_VAAPI || format == AV_PIX_FMT_DRM_PRIME)) {
            std::cout << "prime: " << format << std::endl;
            return true;
        }
        
    if (getTextureFormat(format) != SDL_PIXELFORMAT_UNKNOWN) {
        std::cout << "get texture format: " << format << std::endl;
        return true;
    }
    return false;
}

enum AVPixelFormat getSupportedPixelFormat(AVCodecContext* s, const enum AVPixelFormat* pix_fmts)
{
    const enum AVPixelFormat *p;

    for (p = pix_fmts; *p != AV_PIX_FMT_NONE; p++) {
        const AVPixFmtDescriptor *desc = av_pix_fmt_desc_get(*p);

        if (!(desc->flags & AV_PIX_FMT_FLAG_HWACCEL)) {
            /* We support all memory formats using swscale */
            break;
        }

        if (isSupportedPixelFormat(*p)) {
            /* We support this format */
            break;
        }
    }

    if (*p == AV_PIX_FMT_NONE) {
        SDL_Log("Couldn't find a supported pixel format:\n");
        for (p = pix_fmts; *p != AV_PIX_FMT_NONE; p++) {
            SDL_Log("    %s\n", av_get_pix_fmt_name(*p));
        }
    }

    return *p;
}
