zwodev/vm1-video-mixer/vm1/cpp/source/MediaPlayer.cpp

/*
 * Copyright (c) 2023-2026 Nils Zweiling & Julian Jungel
 *
 * This file is part of VM-1 which is released under the MIT license.
 * See file LICENSE or go to https://github.com/zwodev/vm1-video-mixer/tree/master/LICENSE
 * for full license details.
 */

#include "MediaPlayer.h"

#include <SDL3/SDL_opengl.h>
#include <SDL3/SDL_opengles2.h>
#include <EGL/eglext.h>
#include <GLES3/gl31.h>

MediaPlayer::MediaPlayer()
{
}

MediaPlayer::~MediaPlayer()
{
    if (m_vbo) {
        glDeleteBuffers(1, &m_vbo);
        m_vbo = 0;
    }
    if (m_vao) {
        glDeleteVertexArrays(1, &m_vao);
        m_vao = 0;
    }
}

void MediaPlayer::play()
{
    reset();
    m_audioQueue.setActive(true);
    m_videoQueue.setActive(true);
    m_isRunning = true;
    m_decoderThread = std::thread(&MediaPlayer::run, this);
}

bool MediaPlayer::isFrameReady() {
    return m_videoQueue.isFrameReady();
}

GLuint MediaPlayer::texture()
{
    return m_rgbTexture;
}

void MediaPlayer::close()
{
    m_isRunning = false;
    m_videoQueue.setActive(false);
    m_audioQueue.setActive(false);
    
    if (m_decoderThread.joinable()) {
        m_decoderThread.join();
    }

    if (m_audio) {
        m_audio->unbindAndDestroy();
        m_audio = nullptr;
    }
    
    EGLDisplay display = eglGetCurrentDisplay();
    if (m_fence != EGL_NO_SYNC) {
        eglClientWaitSync(display, m_fence, EGL_SYNC_FLUSH_COMMANDS_BIT, EGL_FOREVER);
        eglDestroySync(display, m_fence);
        m_fence = EGL_NO_SYNC;
    }

    m_videoQueue.clearFrames();
    m_audioQueue.clearFrames();
}

void MediaPlayer::reset()
{
    //
}

void MediaPlayer::createVertexBuffers()
{   
    float quadVertices[] = {
        //  x,    y,    u,   v
        -1.0f, -1.0f,  0.0f, 0.0f, // bottom left
        1.0f, -1.0f,  1.0f, 0.0f, // bottom right
        1.0f,  1.0f,  1.0f, 1.0f, // top right

        -1.0f, -1.0f,  0.0f, 0.0f, // bottom left
        1.0f,  1.0f,  1.0f, 1.0f, // top right
        -1.0f,  1.0f,  0.0f, 1.0f  // top left
    };

    // Setup VAO, VBO, and attribute pointers for aPos (vec2) and aTexCoord (vec2)
    glGenVertexArrays(1, &m_vao);
    glGenBuffers(1, &m_vbo);

    glBindVertexArray(m_vao);
    glBindBuffer(GL_ARRAY_BUFFER, m_vbo);
    glBufferData(GL_ARRAY_BUFFER, sizeof(quadVertices), quadVertices, GL_STATIC_DRAW);

    // Position
    glVertexAttribPointer(0, 2, GL_FLOAT, GL_FALSE, 4 * sizeof(float), (void*)0);
    glEnableVertexAttribArray(0);
   
    // Texture coordinates
    glVertexAttribPointer(1, 2, GL_FLOAT, GL_FALSE, 4 * sizeof(float), (void*)(2 * sizeof(float)));
    glEnableVertexAttribArray(1);

    glBindBuffer(GL_ARRAY_BUFFER, 0);
    glBindVertexArray(0);
}

void MediaPlayer::initializeFramebufferAndTextures()
{
    // Generate input buffer (SAND128 NV12 / YUV)
    for (int i = 0; i < m_numberOfInputImages; ++i) {
        GLuint texId;
        glGenTextures(1, &texId);
        m_yuvTextures.push_back(texId);
        m_yuvImages.push_back(EGL_NO_IMAGE);
    }
    
    // Generate and bind the output framebuffer (RGB)
    glGenFramebuffers(1, &m_frameBuffer);
    glBindFramebuffer(GL_FRAMEBUFFER, m_frameBuffer);

    // Create output texture (RGB)
    glGenTextures(1, &m_rgbTexture);
    glBindTexture(GL_TEXTURE_2D, m_rgbTexture);
    glTexParameteri(GL_TEXTURE_2D, GL_TEXTURE_WRAP_S, GL_CLAMP_TO_EDGE);
    glTexParameteri(GL_TEXTURE_2D, GL_TEXTURE_WRAP_T, GL_CLAMP_TO_EDGE);
    glTexParameteri(GL_TEXTURE_2D, GL_TEXTURE_MAG_FILTER, GL_LINEAR);
    glTexParameteri(GL_TEXTURE_2D, GL_TEXTURE_MIN_FILTER, GL_LINEAR); 
    glTexStorage2D(GL_TEXTURE_2D, 1, GL_RGBA8, 1920, 1080);
    glFramebufferTexture2D(GL_FRAMEBUFFER, GL_COLOR_ATTACHMENT0, GL_TEXTURE_2D, m_rgbTexture, 0);

    if (glCheckFramebufferStatus(GL_FRAMEBUFFER) != GL_FRAMEBUFFER_COMPLETE)
        std::cout << "ERROR::FRAMEBUFFER:: Framebuffer is not complete!" << std::endl;

    glBindFramebuffer(GL_FRAMEBUFFER, 0);
    glBindTexture(GL_TEXTURE_2D, 0);
}

// void MediaPlayer::setPlaneId(int planeId)
// {
//     m_planeId = planeId;
// }

// int MediaPlayer::planeId()
// {
//     return m_planeId;
// }
