zwodev/vm1-video-mixer/vm1/cpp/source/PlaybackOperator.h

/*
 * Copyright (c) 2023-2026 Nils Zweiling & Julian Jungel
 *
 * This file is part of VM-1 which is released under the MIT license.
 * See file LICENSE or go to https://github.com/zwodev/vm1-video-mixer/tree/master/LICENSE
 * for full license details.
 */

#pragma once

#include "PlaneRenderer.h"
#include "WebcamPlayer.h"
#include "VideoPlayer.h"
#include "ShaderPlayer.h"
#include "AudioSystem.h"
#include "DeviceController.h"
#include "Registry.h"
#include "EventBus.h"

#include <vector>
#include <map>

class PlaneMixer {
public:

    std::vector<int> activeIds()
    {
        std::vector<int> ids;
        if (m_fromId >= 0) ids.push_back(m_fromId);
        if (m_toId >= 0) ids.push_back(m_toId);
        return ids;
    }

    int fromId()
    {
        return m_fromId;
    }

    int toId()
    {
        return m_toId;
    }

    float fadeTime() const
    {
        return m_fadeTime;
    }

    void setFadeTime(int fadeTime)
    {
        m_fadeTime = fadeTime;
    }

    void setMixValue(float value) {
        m_mixValue = value;
    }

    float mixValue() const
    {
        return m_mixValue;
    }

    void activate()
    {
        if (m_isFading) m_isActive = true;
    }
    
    void reset()
    {
        m_isActive = false;
        m_toId = -1;
        m_fromId = -1;
        m_mixValue = 0.0f;
    }

    bool startFade(int toId)
    {
        if (m_isFading && m_isActive) return false;

        m_toId = toId;
        m_isFading = true;
        m_fadeDir = 1.0f;
        if (m_mixValue > 0.0f) m_fadeDir = -1.0f;

        return true;
    }

    void updateAutoFade(float deltaTime)
    {
        if (!m_isFading || !m_isActive) return;
        
        m_mixValue = m_mixValue + ((deltaTime / m_fadeTime) * m_fadeDir);
        
        if (m_mixValue <= 0.0f) {
            m_mixValue = 0.0f;
            m_isFading = false;
            m_fromId = m_toId;
            m_toId = -1;
        } 
        else if (m_mixValue >= 1.0f) {
            m_mixValue = 0.0f;
            m_isFading = false;
            m_isActive = false;
            m_fromId = m_toId;
            m_toId = -1;
        }
    }

private:
    bool m_isActive = false;
    bool m_isFading = false;
    float m_fadeTime = 2.0f;
    float m_fadeDir = 1.0f;
    float m_mixValue = 0.0f;
    int m_fromId = -1;
    int m_toId = -1;
};

class PlaybackOperator {
public:
    PlaybackOperator(Registry& registry, EventBus& eventBus, DeviceController& deviceController);
    ~PlaybackOperator();

    void initialize();
    void finalize();
    void showMedia(int mediaId);
    void update(float deltaTime);
    void renderPlane(int hdmiId);
    
private:

    void subscribeToEvents();
    void reloadPlaneShader(int planeId);
    bool getWebcamPlayerIdFromPort(int port, int& id);
    bool getFreeVideoPlayerId(int& id, int planeId);
    bool getFreeShaderPlayerId(int& id, int planeId);
    bool isPlayerIdActive(int playerId);
    void updateDeviceController();

private:
    Registry& m_registry;
    EventBus& m_eventBus;
    DeviceController& m_deviceController;
    
    AudioSystem m_audioSystem;
    std::vector<PlaneMixer> m_planeMixers;
    std::vector<PlaneRenderer*> m_planeRenderers;
    std::vector<AudioStream*> m_audioStreams;

    std::vector<VideoPlayer*> m_videoPlayers;
    std::vector<WebcamPlayer*> m_webcamPlayers;
    std::vector<ShaderPlayer*> m_shaderPlayers;
    std::vector<MediaPlayer*> m_mediaPlayers;
    //std::map<int, int> m_mediaSlotIdToPlayerId;
    std::vector<int> m_recentlyUsedPlayerIds;

    bool m_isInitialized = false;
    int m_selectedEditButton = -1;
    int m_selectedMediaButton = -1;

};
