zwodev/vm1-video-mixer/vm1/cpp/source/VideoPlayer.h

/*
 * Copyright (c) 2023-2026 Nils Zweiling & Julian Jungel
 *
 * This file is part of VM-1 which is released under the MIT license.
 * See file LICENSE or go to https://github.com/zwodev/vm1-video-mixer/tree/master/LICENSE
 * for full license details.
 */


#pragma once

#include "source/MediaPlayer.h"
#include "source/Shader.h"

#include <SDL3/SDL.h>
#include <SDL3/SDL_render.h>
#include <SDL3/SDL_egl.h>

#include <iostream>
#include <string>
#include <vector>
#include <thread>
#include <mutex>
#include <atomic>
#include <queue>
#include <condition_variable>

extern "C"
{
#include <libavcodec/avcodec.h>
#include <libavformat/avformat.h>
#include <libavutil/avutil.h>
#include <libavutil/pixdesc.h>
#include <libswscale/swscale.h>
#include <libavutil/hwcontext_drm.h>
}


SDL_PixelFormat getTextureFormat(enum AVPixelFormat format);
bool isSupportedPixelFormat(enum AVPixelFormat format);
enum AVPixelFormat getSupportedPixelFormat(AVCodecContext* s, const enum AVPixelFormat* pix_fmts);


class VideoPlayer : public MediaPlayer {
public:
    VideoPlayer();
    ~VideoPlayer();

    void setInPoint(double value);
    double inPoint();
    void setOutPoint(double value);
    double outPoint();
    double currentTime() const { return m_currentTime; } 
    double fps() const { return m_fps; }
    double duration() const { return m_duration; }

    bool openFile(const std::string& fileName, AudioStream* audioStream = nullptr) override;
    void close() override;
    void setLooping(bool looping);
    void update() override;
    void pause(bool isPaused) override;
    
private:
    void reset() override;
    void loadShaders() override;
    void run() override;
    void render();
    void seekToInPoint(bool backward = false);
    

    AVCodecContext* openVideoStream();
    AVCodecContext* openAudioStream();
    void handleAudioFrame(AVFrame* frame);
    bool getTextureForDRMFrame(AVFrame* frame, VideoFrame& dstFrame);


private:
    int m_width = 0;
    int m_height = 0;
    double m_inPoint = 0.0;    // in seconds
    double m_outPoint = -1.0;  // in seconds

    // FFMpeg
    Uint64 m_startTime = 0;
    Uint64 m_pauseStartTime = 0;
    double m_duration = 0.0;
    double m_firstPts = -1.0;
    double m_firstAudioPts = -1.0;
    double m_fps = -1.0;
    double m_currentTime = 0; // in seconds
    AVFormatContext* m_formatContext = nullptr;
    //AVDictionary* m_options = nullptr;
    const AVCodec* m_audioCodec = nullptr;
    const AVCodec* m_videoCodec = nullptr;
    AVCodecContext* m_audioContext = nullptr;
    AVCodecContext* m_videoContext = nullptr;
    AVPacket* m_packet = nullptr;
    AVFrame*  m_frame = nullptr;
    int m_videoStream = -1;
    int m_audioStream = -1;
    bool m_foundKeyframe = false;

    // State
    std::atomic<bool> m_isLooping = false;
    std::atomic<bool> m_isFlushing = false;
};
