zwodev/vm1-video-mixer/vm1/cpp/source/MediaPlayer.h

/*
 * Copyright (c) 2023-2026 Nils Zweiling & Julian Jungel
 *
 * This file is part of VM-1 which is released under the MIT license.
 * See file LICENSE or go to https://github.com/zwodev/vm1-video-mixer/tree/master/LICENSE
 * for full license details.
 */

#pragma once

#include "Shader.h"
#include "ThreadableQueue.h"
#include "AudioDevice.h"
#include "Buffer.h"

#include <SDL3/SDL.h>
#include <SDL3/SDL_render.h>
#include <SDL3/SDL_egl.h>

#include <iostream>
#include <string>
#include <vector>
#include <thread>
#include <mutex>
#include <atomic>
#include <queue>
#include <condition_variable>

struct VideoFrame {
    EGLImage image = EGL_NO_IMAGE;

    bool isFirstFrame = false;
    double pts = 0.0;         // relative to first decoded frame, used for frame scheduling
    double absolutePts = 0.0; // absolute position in the video file, used for display
    int index = -1;
    Buffer* buffer = nullptr;
    
    std::vector<uint32_t> formats;
    std::vector<int> widths;
    std::vector<int> heights;
    std::vector<int> fds;
    std::vector<uint32_t> offsets;
    std::vector<uint32_t> pitches;
};

struct AudioFrame {
    bool isFirstFrame = false;
    double pts = 0.0;
    SDL_AudioSpec spec{};
    std::vector<Uint8> data;
};

class MediaPlayer {

public:
    MediaPlayer();
    virtual ~MediaPlayer();
    
public:
    virtual bool openFile(const std::string& fileName = std::string(), AudioStream* audioStream = nullptr) = 0;
    void play();
    virtual void close();
    void setDevicePath(const std::string& devicePath);
    bool isPlaying() const { return m_isRunning; }
    virtual void pause(bool isPaused) { m_isPaused = isPaused; };
    virtual void update() = 0;
    virtual bool isFrameReady();
    GLuint texture();
    //void setPlaneId(int planeId);
    //int planeId();

protected:
    void createVertexBuffers();
    void initializeFramebufferAndTextures();
    virtual void loadShaders() = 0;
    virtual void run() = 0;
    virtual void reset();

private: 
    void clearFrames();

protected:
    std::atomic<bool> m_isRunning = false;
    std::atomic<bool> m_isPaused = false;
    int m_numberOfInputImages = 1;

    GLuint m_vao; 
    GLuint m_vbo;

    AudioStream* m_audio = nullptr;

    std::thread m_decoderThread;
    ThreadableQueue<VideoFrame> m_videoQueue;
    ThreadableQueue<AudioFrame> m_audioQueue;
    EGLSyncKHR m_fence = EGL_NO_SYNC;
    
    GLuint m_frameBuffer = 0;
    GLuint m_rgbTexture = 0;
    Shader m_shader;

    std::vector<GLuint> m_yuvTextures;
    std::vector<EGLImage> m_yuvImages;

    int m_planeId = 0;
};
