zwodev/vm1-video-mixer/vm1/cpp/source/WebcamPlayer.h

/*
 * Copyright (c) 2023-2026 Nils Zweiling & Julian Jungel
 *
 * This file is part of VM-1 which is released under the MIT license.
 * See file LICENSE or go to https://github.com/zwodev/vm1-video-mixer/tree/master/LICENSE
 * for full license details.
 */


#pragma once

#include "MediaPlayer.h"
#include "Buffer.h"
#include "Shader.h"
#include "CaptureType.h"

#include <SDL3/SDL_render.h> 
#include <SDL3/SDL_opengl.h>
#include <SDL3/SDL_opengles2.h>
#include <SDL3/SDL_egl.h>

#include <linux/videodev2.h>

#include <vector>

struct CameraMode {
    __u32 pixelformat;
    __u32 width;
    __u32 height;
    __u32 interval_num;   // Frame interval numerator
    __u32 interval_den;   // Frame interval denominator
};

class WebcamPlayer : public MediaPlayer {
public: 
    WebcamPlayer();
    ~WebcamPlayer();

public:
    bool openFile(const std::string& fileName, AudioStream* audioStream = nullptr);
    void close() override;
    void finalize();
    void update() override;

    // TODO: Needs to be determined by HDMI port oder dev (/dev/video0)
    int getPort() { return m_port; }
    void setPort(int port) { m_port = port; }  
    void setCaptureType(CaptureType captureType) { m_captureType = captureType; };

private:
    void loadShaders() override;
    void run() override;
    void render();

    void lockBuffer();
    Buffer* getBuffer();
    void unlockBuffer();
    
    bool setCameraMode(int fd, const CameraMode &mode);
    bool setFormat(int fd);
    bool initBuffers(int fd);
    bool queueBuffer(int fd, int index);
    int dequeueBuffer(int fd);
    VideoFrame createFrameFromBuffer(Buffer* buffer);

    void activateShader();
    void deactivateShader();

private:
    CaptureType m_captureType = CaptureType::CT_WEBCAM_NON_ZERO;
    std::string m_devicePath;

    Shader m_webcamShader;
    Shader m_nonZeroCopyWebcamShader;
    GLuint m_nonZeroCopyTextureId;

    int m_port = -1;
    int m_fd = -1;
    int m_bufferIndex = -1;

    v4l2_format m_fmt;
    std::vector<Buffer> m_buffers;
};
