zwodev/vm1-video-mixer/vm1-device/arduino/VM1Device/src/AverageFilter.h

#ifndef AVERAGEFILTER_H
#define AVERAGEFILTER_H

class AverageFilter {
    int maxValues;
    float values[32]; // how many values to take the average from
    float average;

  public:
    AverageFilter() {
      maxValues = sizeof(values) / sizeof(float);
      
      for (int i = 0; i < maxValues; i++) {
        values[i] = 0;
      }
    }

    float Filter(float v) {
      // shift all values one to the left
      for (int i = 0; i < maxValues - 1; i++) {
        values[i] = values[i + 1];
      }
      
      // add current value to the latest index
      values[maxValues - 1] = v;

      // calculate the average
      average = 0;
      for (int i = 0; i < maxValues; i++) {
        average += values[i];
      }
      average /= maxValues;
      
      return average;
    }

};

#endif
