zwodev/vm1-video-mixer/vm1/cpp/tests/compute-shader/main.cpp

/*
 * Copyright (c) 2023-2025 Nils Zweiling & Julian Jungel
 *
 * This file is part of VM-1 which is released under the MIT license.
 * See file LICENSE or go to https://github.com/zwodev/vm1-video-mixer/tree/master/LICENSE
 * for full license details.
 *
 * Parts of this file have been taken from:
 * https://github.com/libsdl-org/SDL/blob/main/test/testffmpeg.c
 *
 */

#include "imgui.h"
#include "imgui_impl_sdl3.h"
#include "imgui_impl_opengl3.h"

#include <stdio.h>
#include <SDL3/SDL.h>
#if defined(IMGUI_IMPL_OPENGL_ES2)
#include <SDL3/SDL_opengles2.h>
#else
#include <SDL3/SDL_opengl.h>
#endif

#include "source/GLHelper.h"
#include "source/CameraController.h"
#include "source/VideoPlayer.h"
#include "source/CameraPlayer.h"


#define USE_OLED

const int FBO_WIDTH = 128;
const int FBO_HEIGHT = 128;

// Main code
int main(int, char **)
{
    // Setup SDL
    if (!SDL_Init(SDL_INIT_VIDEO | SDL_INIT_GAMEPAD))
    {
        printf("Error: SDL_Init(): %s\n", SDL_GetError());
        return -1;
    }

    // Setup OpenGL context for OpenGL ES 3.1
    const char *glsl_version = "#version 300 es";
    SDL_GL_SetAttribute(SDL_GL_CONTEXT_FLAGS, 0);
    SDL_GL_SetAttribute(SDL_GL_CONTEXT_PROFILE_MASK, SDL_GL_CONTEXT_PROFILE_ES);
    SDL_GL_SetAttribute(SDL_GL_CONTEXT_MAJOR_VERSION, 3);
    SDL_GL_SetAttribute(SDL_GL_CONTEXT_MINOR_VERSION, 1);

    // Check number of attached displays
    int x_offsets[2] = { 0, 0 };
    int y_offsets[2] = { 0, 0 };
    int num_displays;
    SDL_DisplayID *displays = SDL_GetDisplays(&num_displays);
    SDL_Log("Found %d display(s)", num_displays);
    for (int i = 0; i < num_displays; ++i)
    {
        SDL_Log("Display ID for %d: %d", i, displays[i]);
        // SDL_DisplayMode mode;
        // if (SDL_GetCurrentDisplayMode(displays[i], &mode) == 0) {
        //     SDL_Log("Display %d native resolution: %dx%d @ %dHz\n",
        //            i, mode.w, mode.h, mode.refresh_rate);
        // }
    }
    SDL_free(displays);

    // Create window with graphics context
    SDL_GL_SetAttribute(SDL_GL_DOUBLEBUFFER, 1);
    SDL_GL_SetAttribute(SDL_GL_DEPTH_SIZE, 24);
    SDL_GL_SetAttribute(SDL_GL_STENCIL_SIZE, 8);

    SDL_PropertiesID props = SDL_CreateProperties();
    if (props == 0)
    {
        SDL_Log("Unable to create properties: %s", SDL_GetError());
        return 0;
    }

    SDL_SetStringProperty(props, SDL_PROP_WINDOW_CREATE_TITLE_STRING, "Window");
    //SDL_SetBooleanProperty(props, SDL_PROP_WINDOW_CREATE_WAYLAND_CREATE_EGL_WINDOW_BOOLEAN, true);
    SDL_SetBooleanProperty(props, SDL_PROP_WINDOW_CREATE_FULLSCREEN_BOOLEAN, true);
    SDL_SetBooleanProperty(props, SDL_PROP_WINDOW_CREATE_OPENGL_BOOLEAN, true);
    SDL_SetNumberProperty(props, SDL_PROP_WINDOW_CREATE_WIDTH_NUMBER, 1920);
    SDL_SetNumberProperty(props, SDL_PROP_WINDOW_CREATE_HEIGHT_NUMBER, 1200);
    SDL_SetNumberProperty(props, SDL_PROP_WINDOW_CREATE_Y_NUMBER, 0);

    std::vector<SDL_Window *> windows;
    for (int i = 0; i < num_displays; ++i)
    {
        // This is the way to associate the second window with the second screen
        // when using the DRM/KMS backend.
        SDL_SetNumberProperty(props, SDL_PROP_WINDOW_CREATE_X_NUMBER, 1920 * i);

        SDL_Window *window = SDL_CreateWindowWithProperties(props);
        if (window == nullptr)
        {
            printf("Error: SDL_CreateWindow(): %s\n", SDL_GetError());
            return -1;
        }
        windows.push_back(window);
    }

    if (windows.size() < 1)
    {
        SDL_Log("Unable to create an SDL window!");
        return 0;
    }

    SDL_GLContext gl_context = SDL_GL_CreateContext(windows[0]);
    if (gl_context == nullptr)
    {
        printf("Error: SDL_GL_CreateContext(): %s\n", SDL_GetError());
        return -1;
    }

    // Enable vsync and activate all windows
    SDL_GL_SetSwapInterval(0);
    for (int i = 0; i < windows.size(); ++i)
    {
        SDL_ShowWindow(windows[i]);
    }

    // Init GL Helper
    bool success = GLHelper::init();
    printf("Success: %d\n", success);

    IMGUI_CHECKVERSION();

    // Setup main context for ImGui (screen)
    ImGuiContext *mainContext = ImGui::CreateContext();
    ImGuiIO &io = ImGui::GetIO();
    (void)io;

    // Setup Platform/Renderer backends for main context
    ImGui_ImplSDL3_InitForOpenGL(windows[0], gl_context);
    ImGui_ImplOpenGL3_Init(glsl_version);

    // Setup Dear ImGui style
    ImGui::StyleColorsDark();

    // Our state
    ImVec4 clear_color = ImVec4(0.45f, 0.55f, 0.60f, 1.00f);

    // TODO: This was not implemented in SDL3 yet. I did it. Another way or PR?
    SDL_RaiseWindow(windows[0]);

    // Camera
    CameraController cameraController;
    cameraController.setup();

    // Camera Player
    CameraPlayer cameraPlayer0;
    cameraPlayer0.openFile("");
    cameraPlayer0.play();

    // Video Player
    VideoPlayer videoPlayer0;
    videoPlayer0.openFile("../../../videos/vm1-introduction-small.mp4");
    videoPlayer0.play();
    videoPlayer0.setLooping(true);

    VideoPlayer videoPlayer1;
    videoPlayer1.openFile("../../../videos/vm1-introduction-small.mp4");
    videoPlayer1.play();
    videoPlayer1.setLooping(true);

    VideoPlayer videoPlayer2;
    videoPlayer2.openFile("../../../videos/vm1-introduction-small.mp4");
    videoPlayer2.play();
    videoPlayer2.setLooping(true);

    VideoPlayer videoPlayer3;
    videoPlayer3.openFile("../../../videos/vm1-introduction-small.mp4");
    videoPlayer3.play();
    videoPlayer3.setLooping(true);

    // Prepared delta time
    Uint64 lastTime = SDL_GetTicks();
    bool isVideoEnabled = true;
    bool isCameraEnabled = false;

    std::string selectedFile;

    // Main loop
    bool done = false;
    while (!done)
    {
        // Calculate delta time
        Uint64 currentTime = SDL_GetTicks();
        double deltaTime = (currentTime - lastTime) / 1000.0;
        lastTime = currentTime;

        // Poll and handle events (inputs, window resize, etc.)
        SDL_Event event;
        while (SDL_PollEvent(&event))
        {
            ImGui_ImplSDL3_ProcessEvent(&event);
            if (event.type == SDL_EVENT_QUIT)
            {
                done = true;
            }
            else if (event.type == SDL_EVENT_WINDOW_CLOSE_REQUESTED && event.window.windowID == SDL_GetWindowID(windows[0]))
            {
                done = true;
            }
        }
        if (SDL_GetWindowFlags(windows[0]) & SDL_WINDOW_MINIMIZED)
        {
            SDL_Delay(10);
            continue;
        }


        // Start the Dear ImGui frame
        ImGui::SetCurrentContext(mainContext);
        ImGui_ImplOpenGL3_NewFrame();
        ImGui_ImplSDL3_NewFrame();
        ImGui::NewFrame();


        // Desktop UI
        // TODO: Put in own class.
        {
            ImGui::Begin("Development");
            ImGui::Text("Application average %.3f ms/frame (%.1f FPS)", 1000.0f / io.Framerate, io.Framerate);
            ImGui::End();
        }

        // Compute Shader Test 
        {
            ImGui::SetNextWindowSize(ImVec2(960, 540));
            ImGui::Begin("Camera 0");
            cameraPlayer0.update();
            ImGui::Image((void *)(intptr_t)cameraPlayer0.texture(), ImVec2(960, 540));
            ImGui::End();
        }

        {
            ImGui::SetNextWindowSize(ImVec2(960, 540));
            ImGui::Begin("Video 0");
            videoPlayer0.update();
            ImGui::Image((void *)(intptr_t)videoPlayer0.texture(), ImVec2(960, 540));
            ImGui::End();
        }

        {
            ImGui::SetNextWindowSize(ImVec2(960, 540));
            ImGui::Begin("Video 1");
            videoPlayer1.update();
            ImGui::Image((void *)(intptr_t)videoPlayer1.texture(), ImVec2(960, 540));
            ImGui::End();
        }

        {
            ImGui::SetNextWindowSize(ImVec2(960, 540));
            ImGui::Begin("Video 2");
            videoPlayer2.update();
            ImGui::Image((void *)(intptr_t)videoPlayer2.texture(), ImVec2(960, 540));
            ImGui::End();
        }

        {
            ImGui::SetNextWindowSize(ImVec2(960, 540));
            ImGui::Begin("Video 3");
            videoPlayer3.update();
            ImGui::Image((void *)(intptr_t)videoPlayer3.texture(), ImVec2(960, 540));
            ImGui::End();
        }

        // Rendering window 0
        SDL_GL_MakeCurrent(windows[0], gl_context);
        ImGui::Render();
        //glViewport(0, 0, (int)io.DisplaySize.x, (int)io.DisplaySize.y);
        glViewport(0, 0, 1920, 1080);
        glClearColor(clear_color.x * clear_color.w, clear_color.y * clear_color.w, clear_color.z * clear_color.w, clear_color.w);
        glClear(GL_COLOR_BUFFER_BIT);

        // Render video content
        // if (isVideoEnabled)
        //     playbackOperator.renderPlane(0, deltaTime);

        ImGui_ImplOpenGL3_RenderDrawData(ImGui::GetDrawData());
        SDL_GL_SwapWindow(windows[0]);
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
